ezcGman/lora-gateway/src/lora-gateway-e32/config.h

const char* wifiSsid     = "YOUR_WIFI_SSID";
const char* wifiPassword = "YOUR_WIFI_PASSWORD";
int wifiChannel = 7;

const char* mqttServer = "YOUR_MQTT_SERVER";
const int mqttPort = 1883;
const char* mqttUser = "YOUR_MQTT_USER";
const char* mqttPassword = "YOUR_MQTT_PASSWORD";
